UVicRocketry/Prepreg-Oven/Wiring Diagram/Oven_Wiring_Layout_v.2.kicad_sch

## KiCad design Wiring Diagram/Oven_Wiring_Layout_v.2.kicad_sch (2022-04-14)

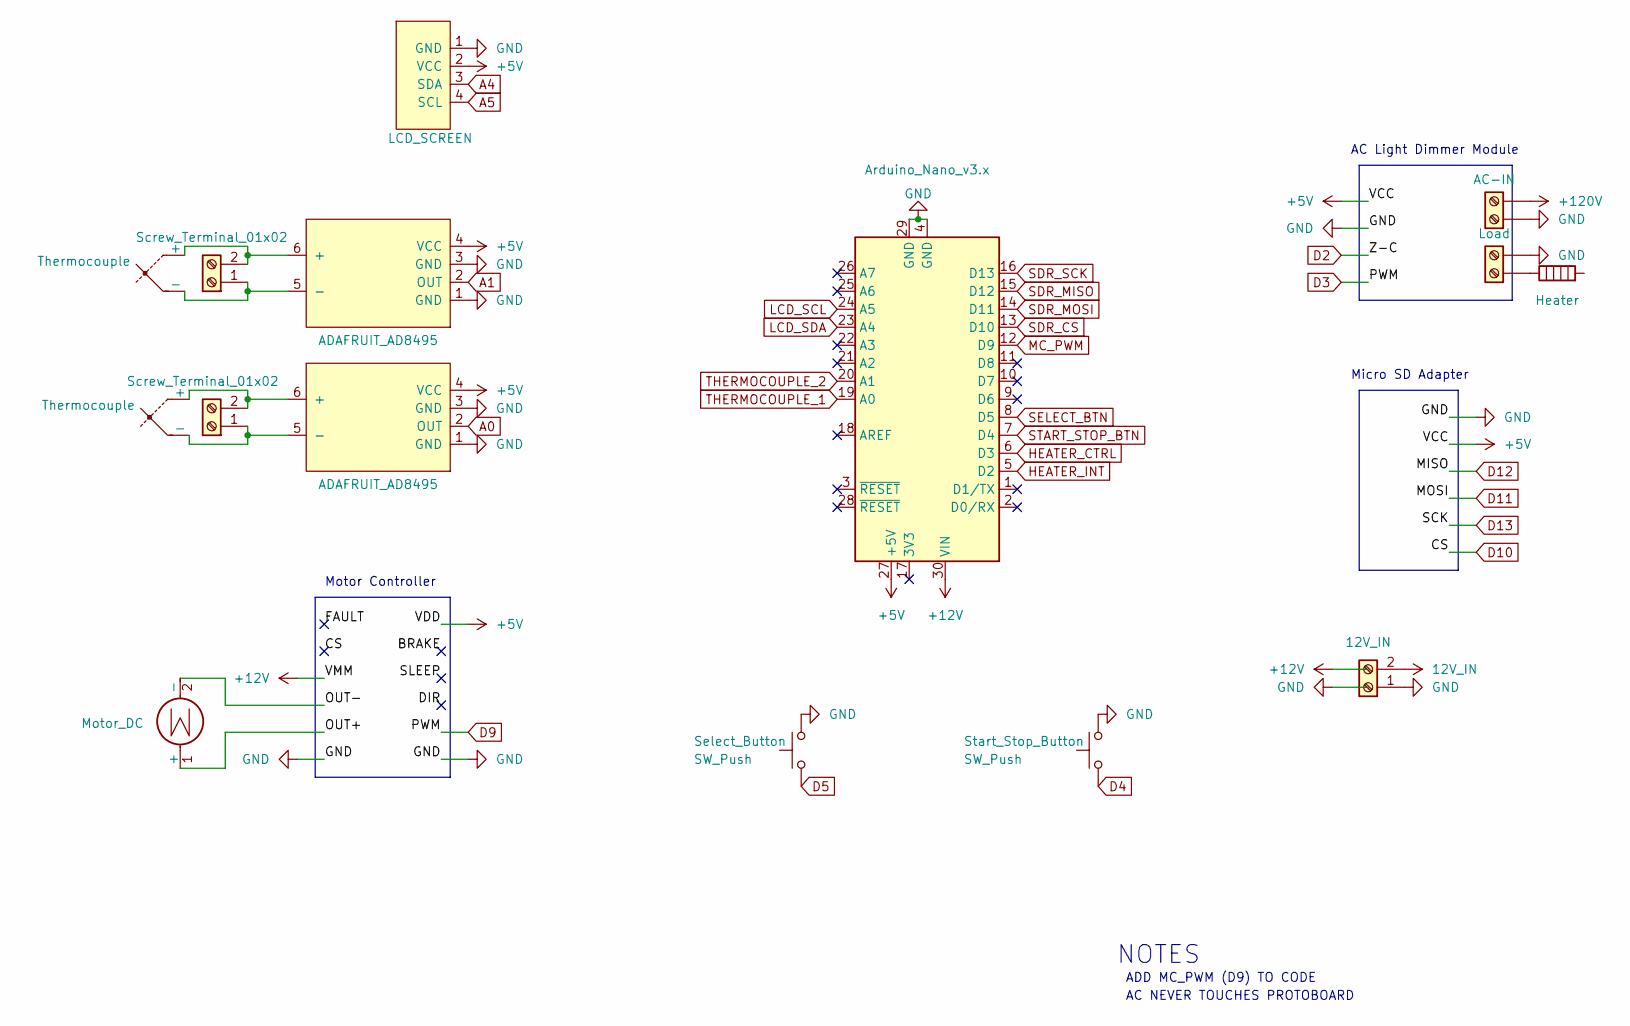
[picture p3: schematic Oven_Wiring_Layout_v.2.kicad_sch]

Parts:
12V_IN: Screw_Terminal_01x02
+120V: +5V
Select_Button: SW_Push
Start_Stop_Button: SW_Push

Connections:
D4: Start_Stop_Button.1
D5: Select_Button.1
unnamed: 12V_IN.1 (+12V), 12V_IN.2

Notes on the sheet:
AC Light Dimmer Module
AC NEVER TOUCHES PROTOBOARD
ADD MC_PWM (D9) TO CODE
Motor Controller
NOTES
Micro SD Adapter
